aricurlind/OmegaTron/doc/classification_files/Akku/2021-04-27 18_49_56-.png

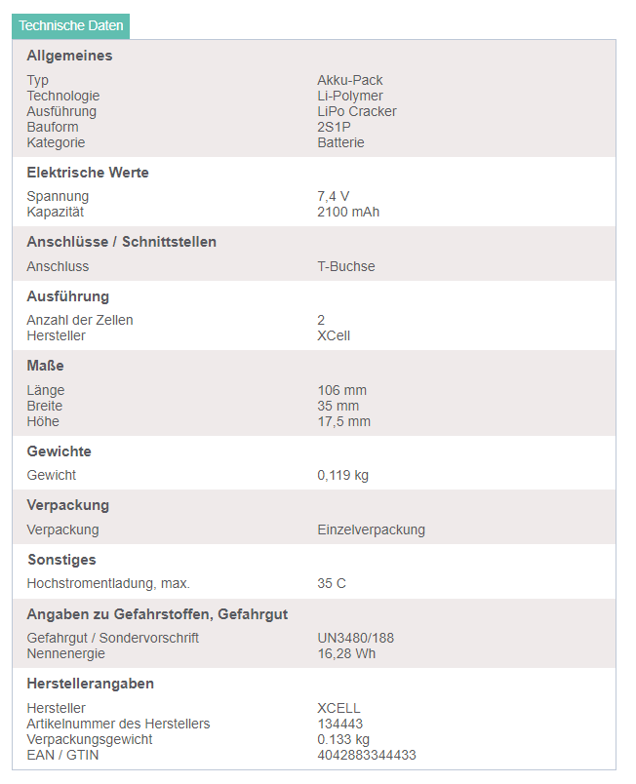
doc/classification_files/Akku/2021-04-27 18_49_56-.png
