aricurlind/OmegaTron/doc/classification_files/Getribe Motor/Motortreiber.png

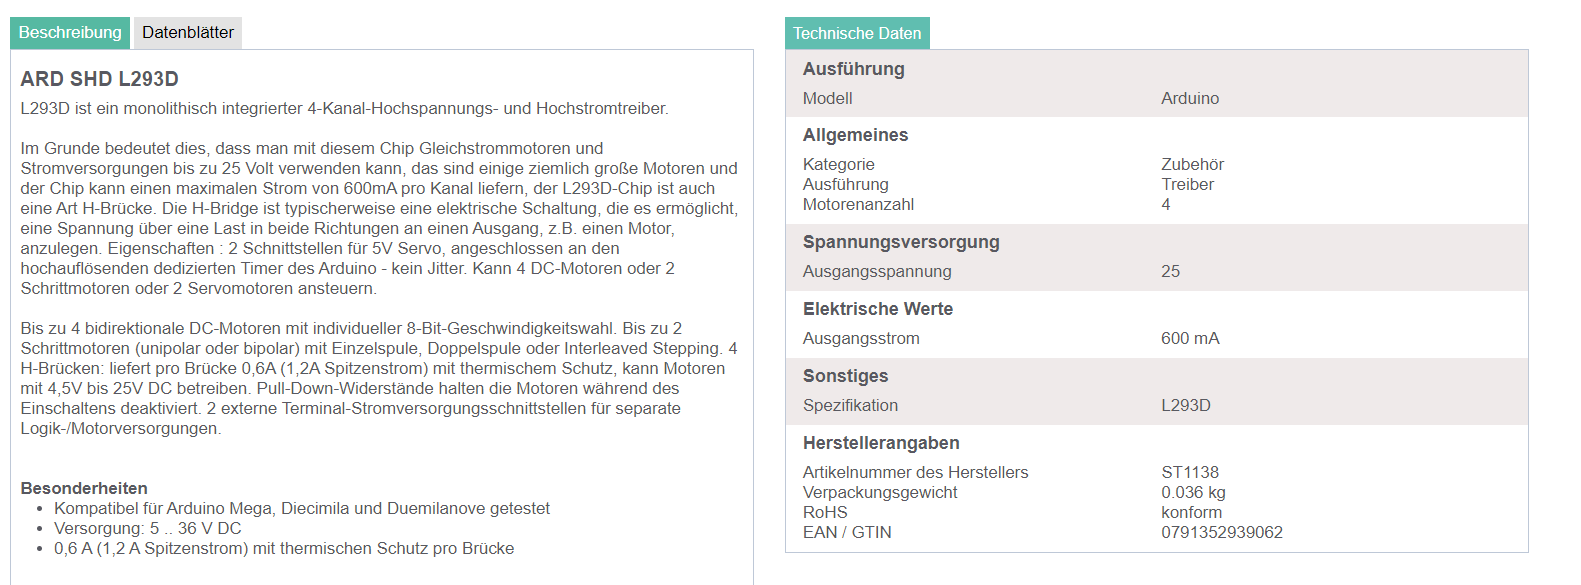
doc/classification_files/Getribe Motor/Motortreiber.png
