aricurlind/OmegaTron/doc/vids_pics/OmegaTron1.jpeg

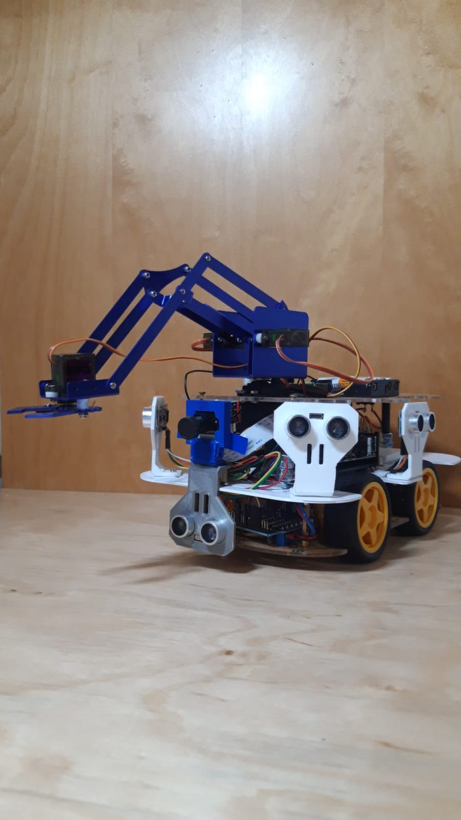
doc/vids_pics/OmegaTron1.jpeg
