aricurlind/OmegaTron/doc/vids_pics/opencv1.png

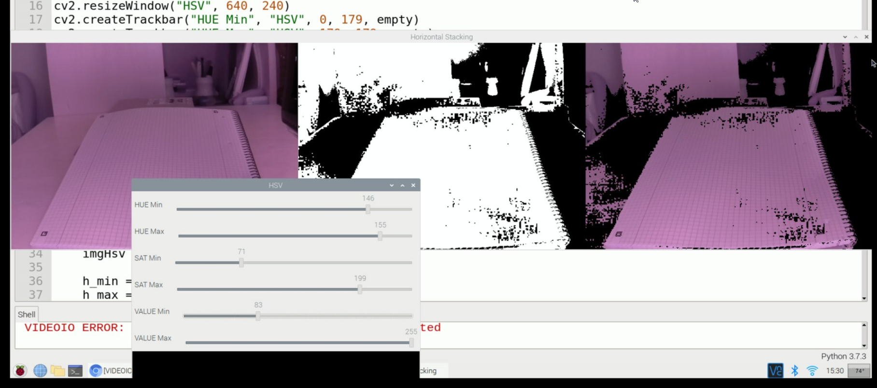
doc/vids_pics/opencv1.png
