aricurlind/OmegaTron/doc/vids_pics/opencv2.png

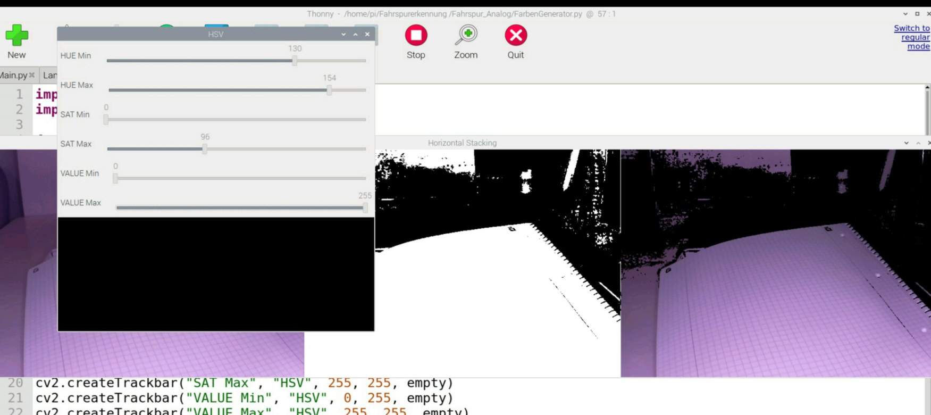
doc/vids_pics/opencv2.png
