aricurlind/OmegaTron/doc/vids_pics/opencv4.png

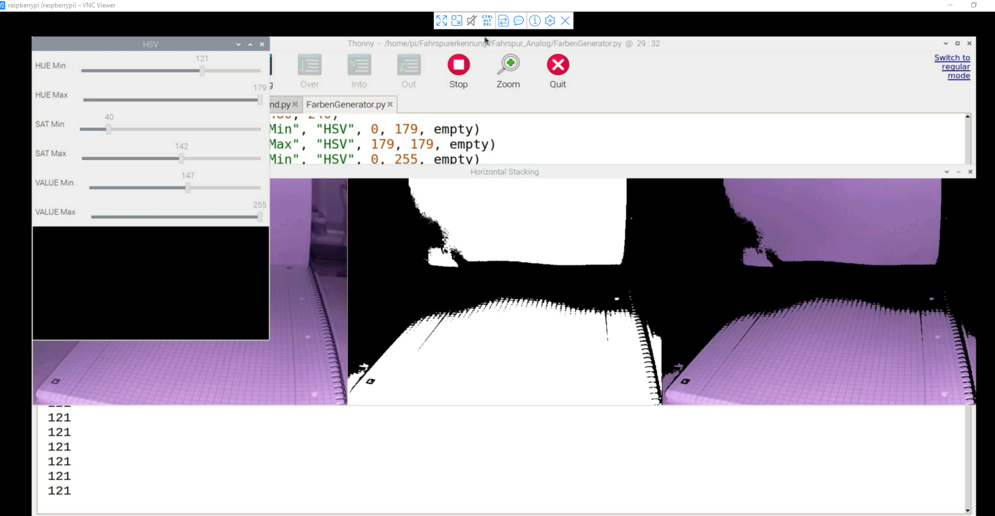
doc/vids_pics/opencv4.png
