aricurlind/OmegaTron/doc/vids_pics/Ultraschall-Raspberry_Steckplatine.jpg

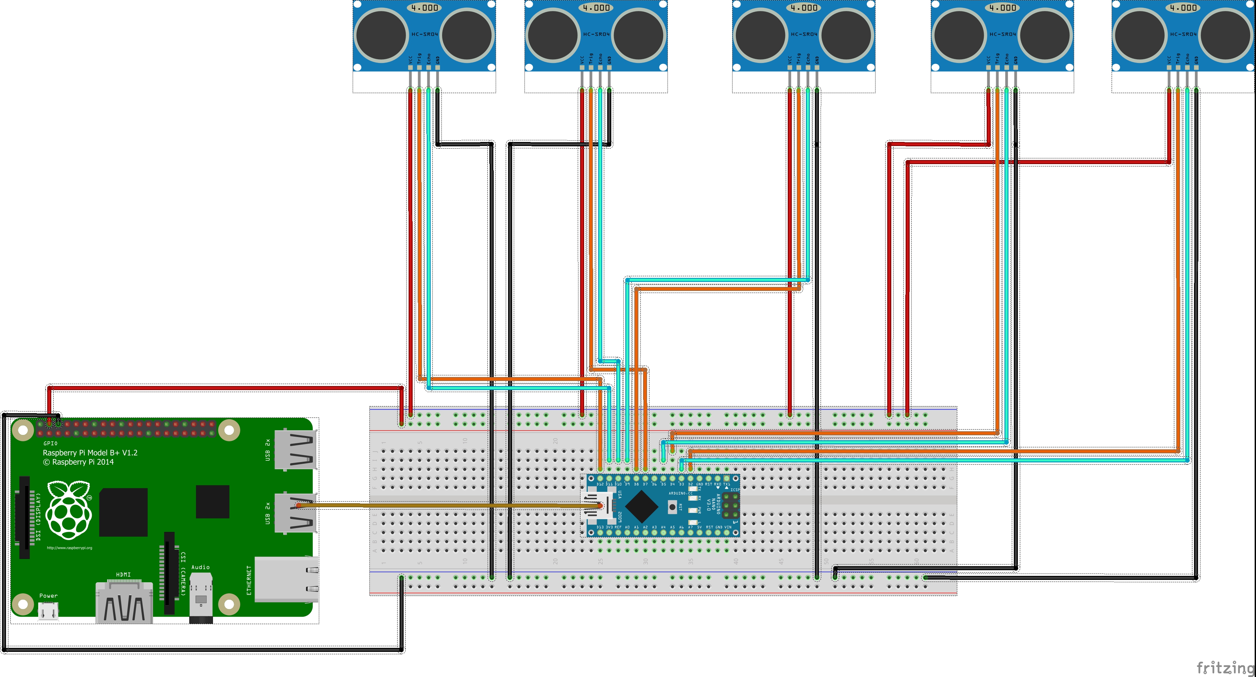
doc/vids_pics/Ultraschall-Raspberry_Steckplatine.jpg
